pilsbot/pilsbot/hw-model/schalter_blende.FCStd

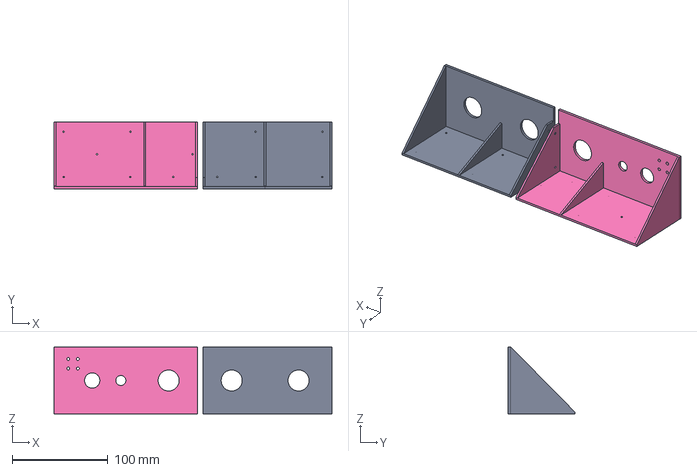
[picture p19: CAD file, 2021-12-27]
hw-model/schalter_blende.FCStd
291.0 x 70.0 x 70.0 mm
DingR
DingL
