pilsbot/pilsbot/hw-model/export/indicator_slots_base.stl

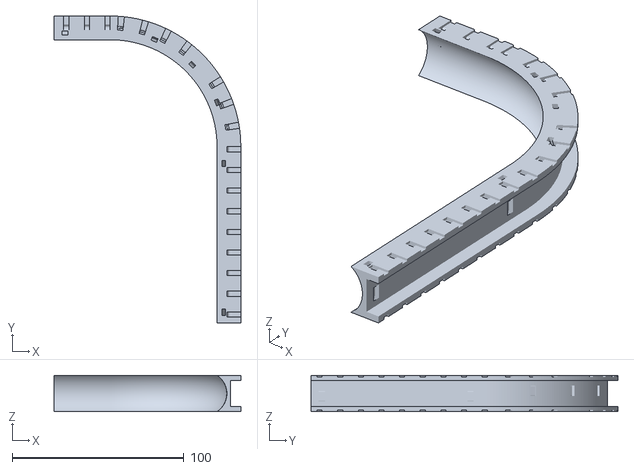
[picture p20: CAD file, 2025-06-03]
hw-model/export/indicator_slots_base.stl
108.5 x 178.5 x 21.0
