pilsbot/pilsbot/hw-model/head_mcu_case.FCStd

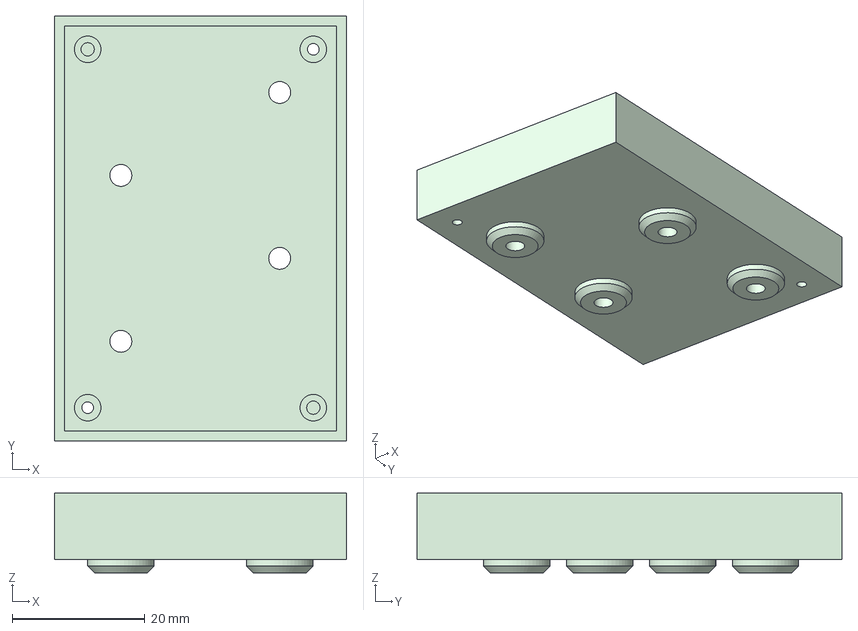
[picture p21: CAD file, 2021-06-11]
hw-model/head_mcu_case.FCStd
44.0 x 64.0 x 12.0 mm
