pilsbot/pilsbot/hw-model/export/indicator_slots_both.stl

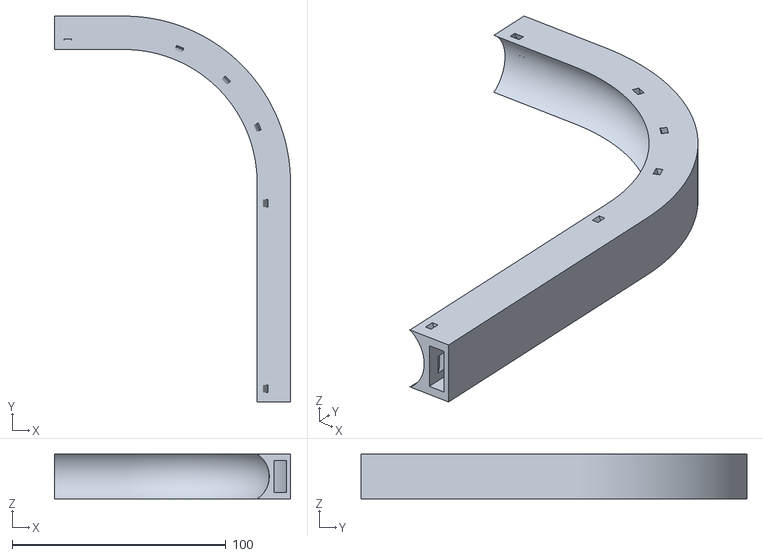
[picture p22: CAD file, 2025-06-03]
hw-model/export/indicator_slots_both.stl
110.3 x 180.3 x 21.0
