pilsbot/pilsbot/hw-model/export/axis_fastener.stl

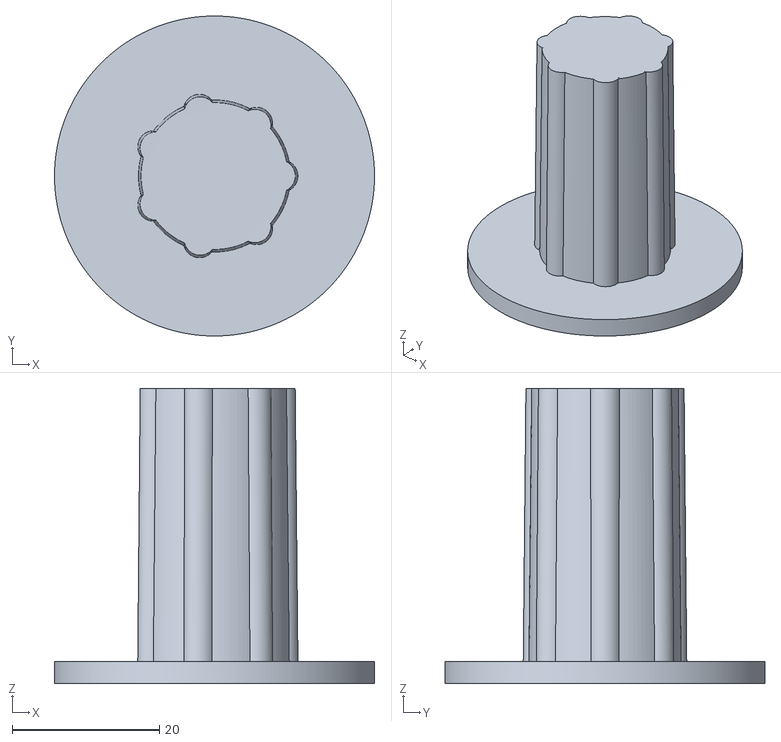
[picture p23: CAD file, 2024-06-01]
hw-model/export/axis_fastener.stl
43.5 x 43.5 x 40.1
