pilsbot/pilsbot/hw-model/export/SSD_holder_logging.stl

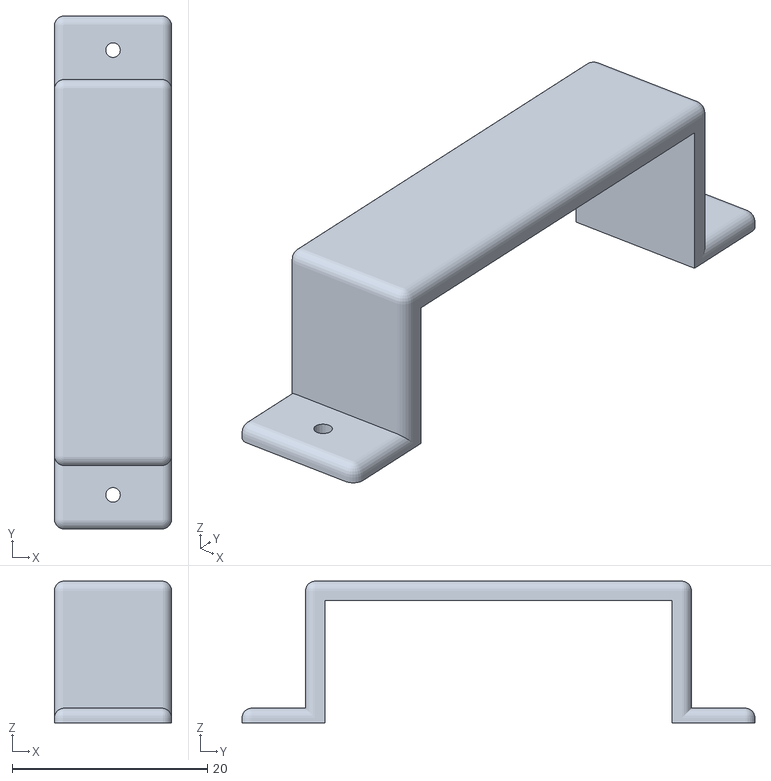
[picture p24: CAD file, 2024-06-01]
hw-model/export/SSD_holder_logging.stl
12.0 x 52.5 x 14.5
