pilsbot/pilsbot/hw-model/export/button_holder.stl

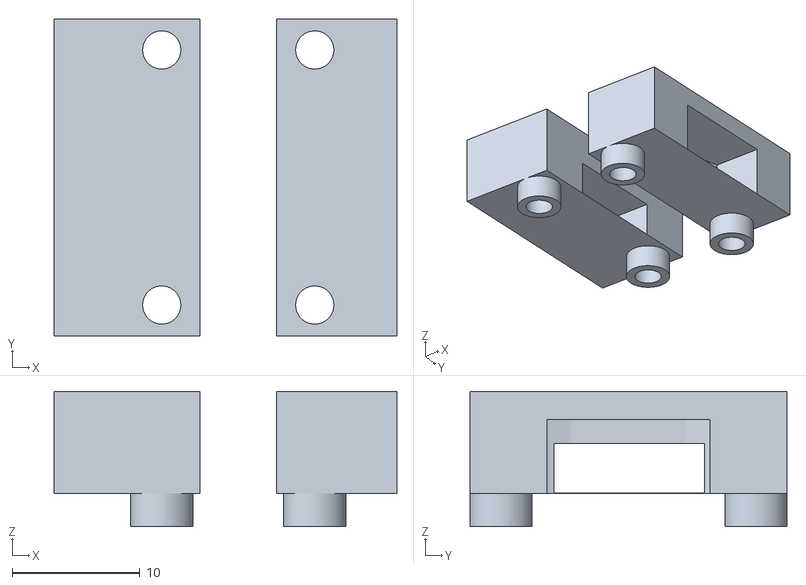
[picture p25: CAD file, 2024-06-01]
hw-model/export/button_holder.stl
26.9 x 24.9 x 10.6
