pilsbot/pilsbot/hw-model/export/antigriff.stl

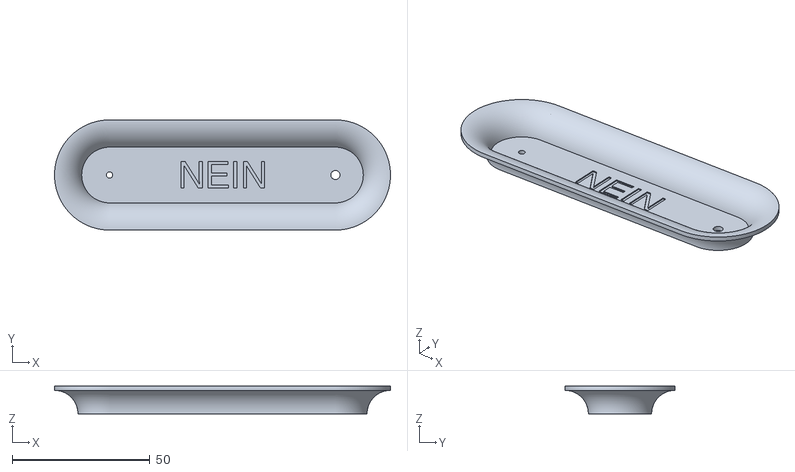
[picture p26: CAD file, 2024-03-05]
hw-model/export/antigriff.stl
122.0 x 40.0 x 10.0
