pilsbot/pilsbot/hw-model/export/steering_encoder_außen.stl

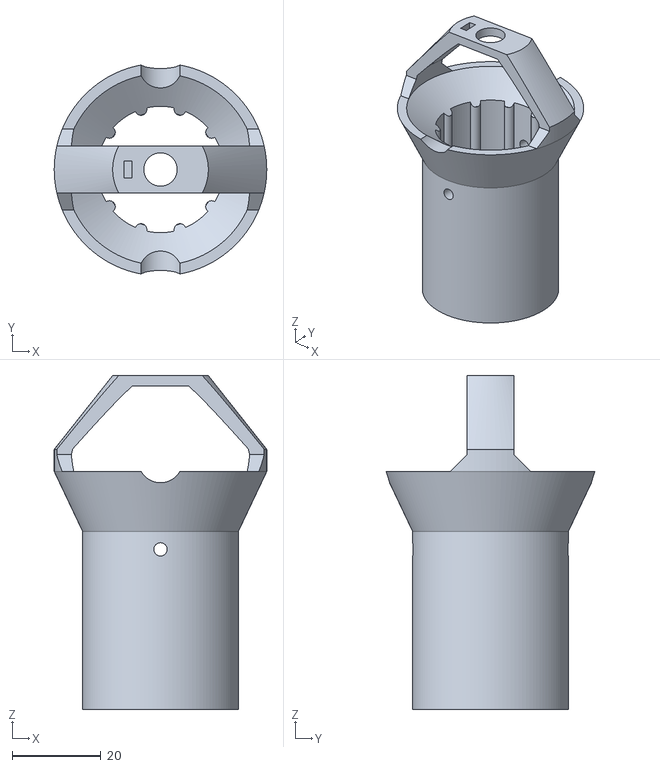
[picture p27: CAD file, 2023-06-13]
hw-model/export/steering_encoder_außen.stl
47.8 x 47.0 x 75.1
