pilsbot/pilsbot/hw-model/export/SSD_holder_root.stl

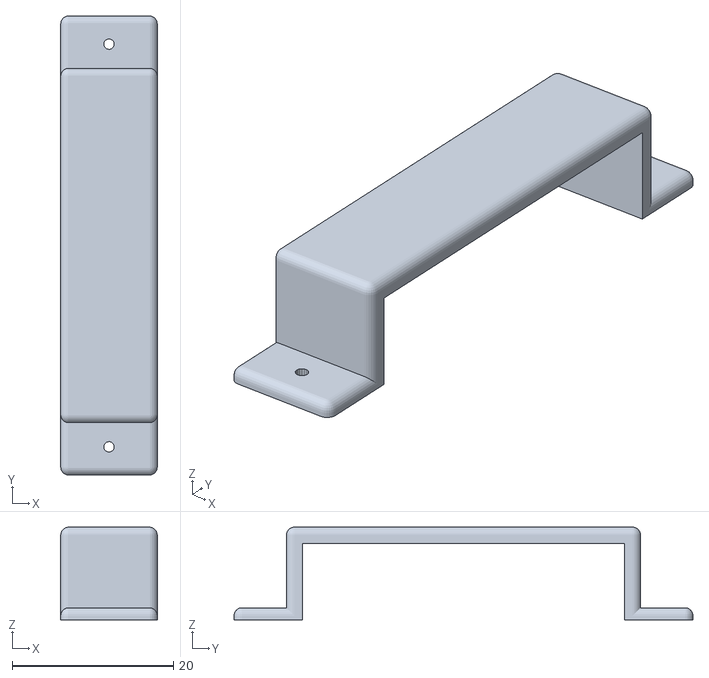
[picture p28: CAD file, 2023-02-14]
hw-model/export/SSD_holder_root.stl
12.0 x 57.0 x 11.5
