pilsbot/pilsbot/hw-model/export/splash_protection_hb_driver-Abdeckung.stl

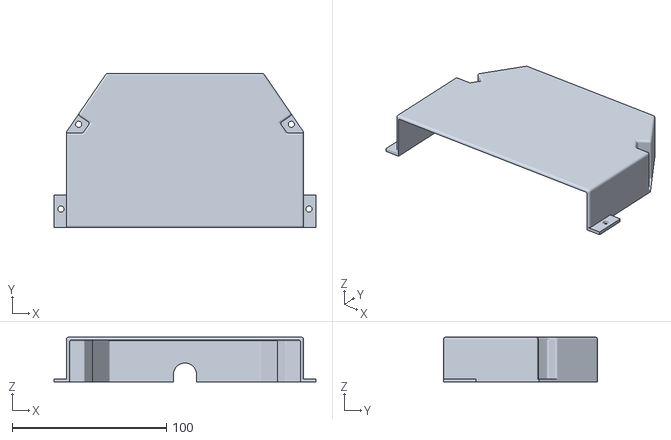
[picture p29: CAD file, 2023-02-14]
hw-model/export/splash_protection_hb_driver-Abdeckung.stl
170.0 x 100.0 x 29.0
