pilsbot/pilsbot/hw-model/export/Raspi-Cam-holder-Deckel.stl

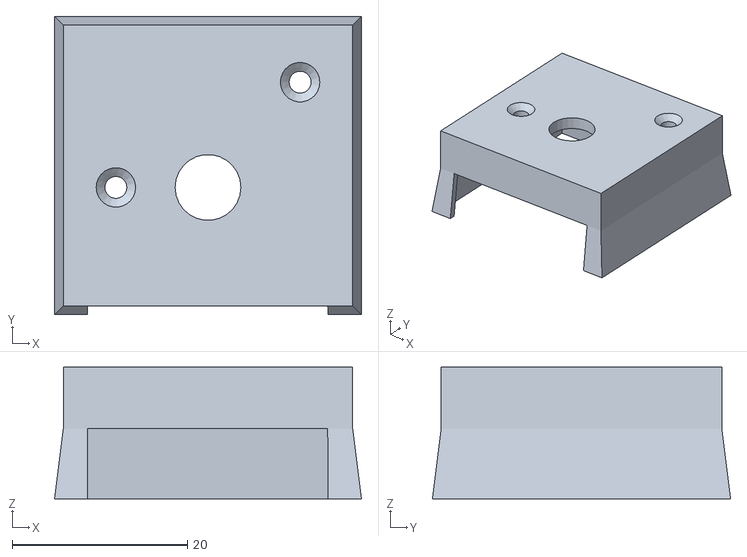
[picture p30: CAD file, 2023-01-29]
hw-model/export/Raspi-Cam-holder-Deckel.stl
35.0 x 34.0 x 15.0
