pilsbot/pilsbot/hw-model/export/water_splash_plate_holder.stl

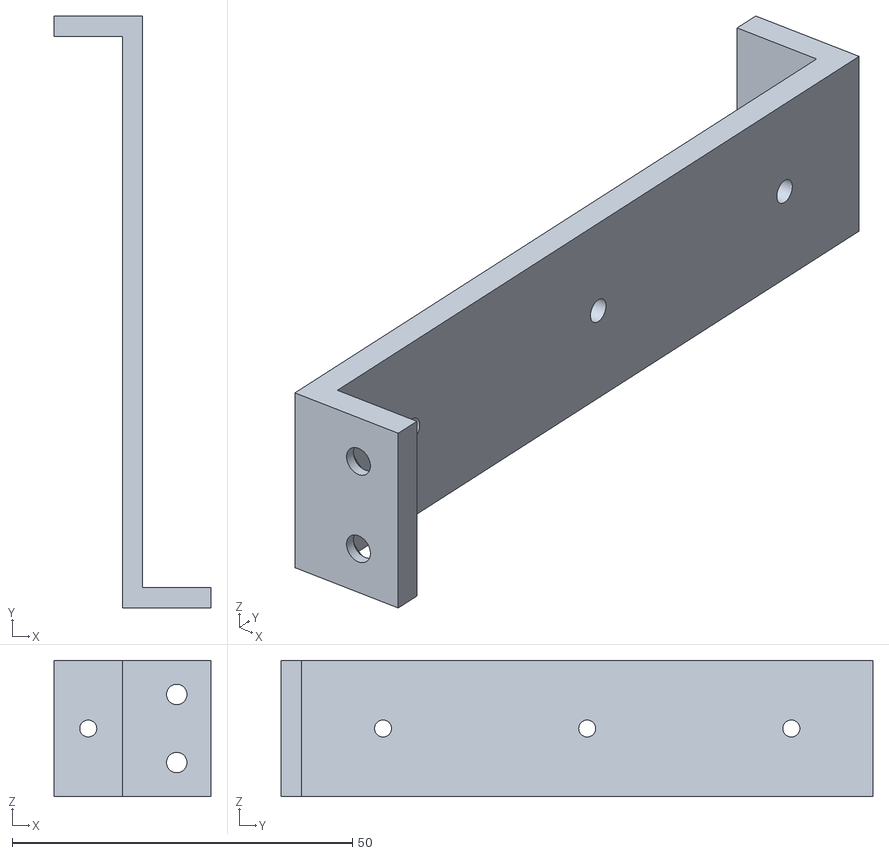
[picture p31: CAD file, 2023-01-28]
hw-model/export/water_splash_plate_holder.stl
23.0 x 87.0 x 20.0
