pilsbot/pilsbot/hw-model/export/bigbattery_holder_front.stl

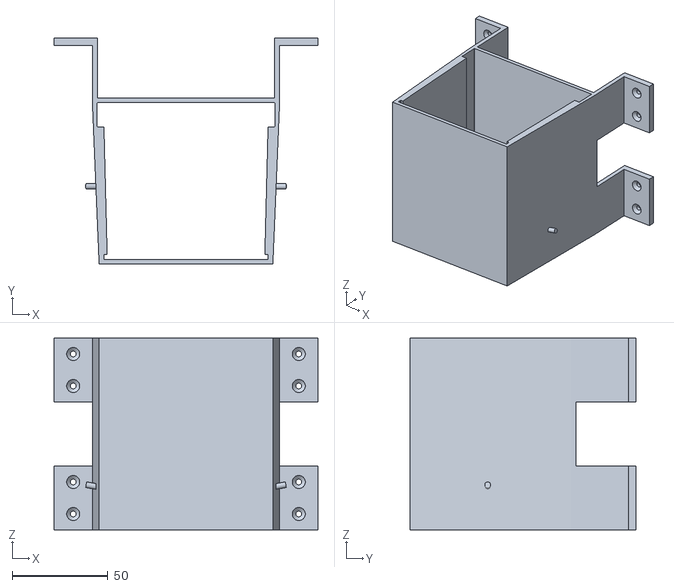
[picture p32: CAD file, 2023-01-28]
hw-model/export/bigbattery_holder_front.stl
137.5 x 117.8 x 100.0
