pilsbot/pilsbot/hw-model/export/bigbattery_holder_back.stl

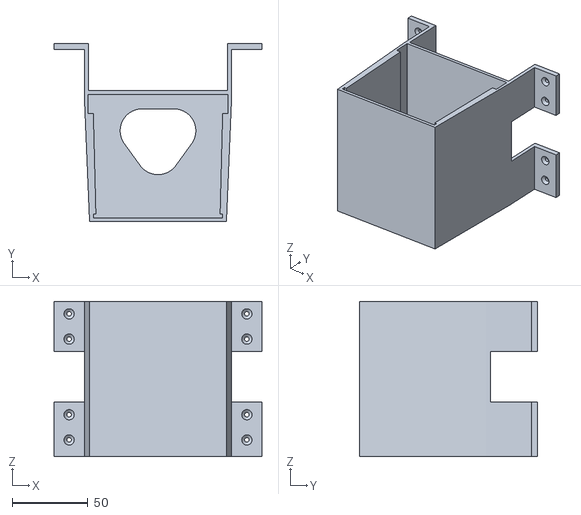
[picture p33: CAD file, 2023-01-28]
hw-model/export/bigbattery_holder_back.stl
137.5 x 117.8 x 102.8
