pilsbot/pilsbot/hw-model/export/battery_cable_strain_protector.stl

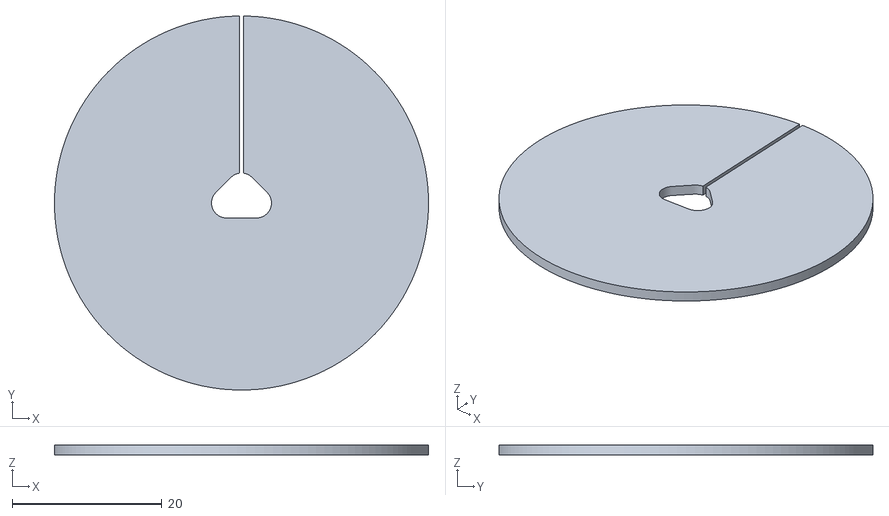
[picture p34: CAD file, 2023-01-21]
hw-model/export/battery_cable_strain_protector.stl
50.0 x 50.0 x 1.40
