pilsbot/pilsbot/hw-model/export/OAK-D_Mount.stl

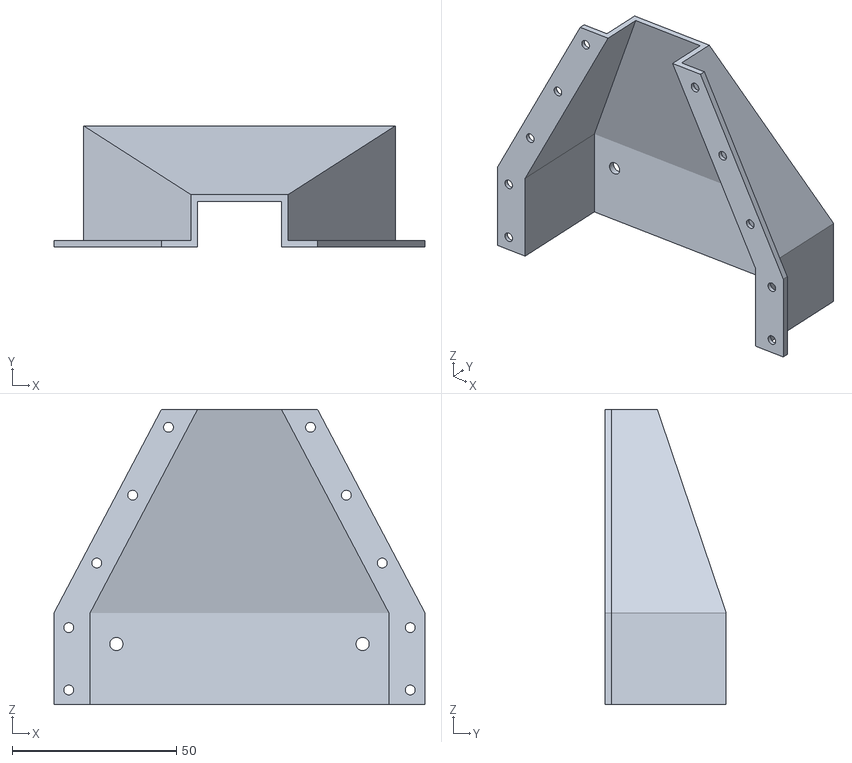
[picture p35: CAD file, 2023-01-19]
hw-model/export/OAK-D_Mount.stl
113.0 x 37.0 x 90.0
