pilsbot/pilsbot/hw-model/export/Raspi-Cam-holder-Counter_ding.stl

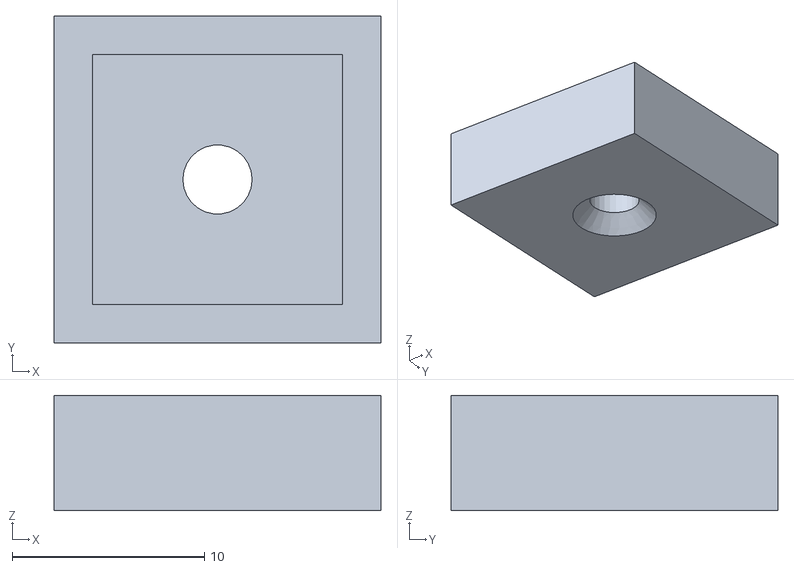
[picture p36: CAD file, 2023-01-08]
hw-model/export/Raspi-Cam-holder-Counter_ding.stl
17.0 x 17.0 x 6.00
