pilsbot/pilsbot/hw-model/export/joystick_receiver_holder.stl

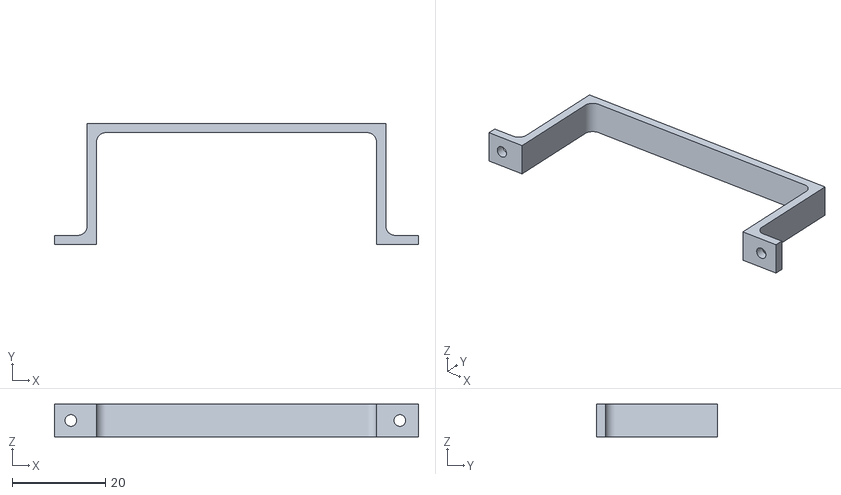
[picture p37: CAD file, 2023-01-08]
hw-model/export/joystick_receiver_holder.stl
78.0 x 26.0 x 7.00
