pilsbot/pilsbot/hw-model/export/steering_encoder_innen.stl

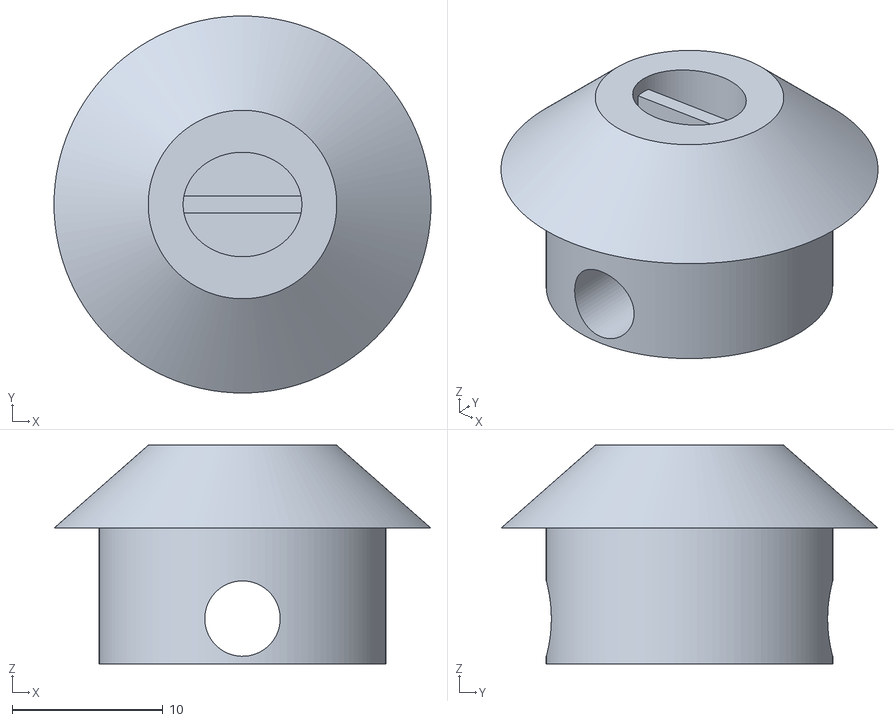
[picture p38: CAD file, 2022-03-26]
hw-model/export/steering_encoder_innen.stl
25.0 x 25.0 x 14.5
