pilsbot/pilsbot/hw-model/export/mountplate_feet.stl

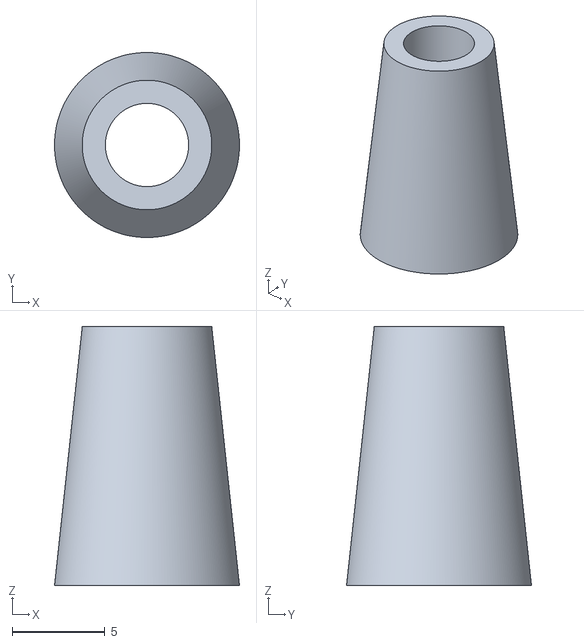
[picture p39: CAD file, 2022-03-26]
hw-model/export/mountplate_feet.stl
10.0 x 10.0 x 14.0
