pilsbot/pilsbot/hw-model/export/schalterblendeR.stl

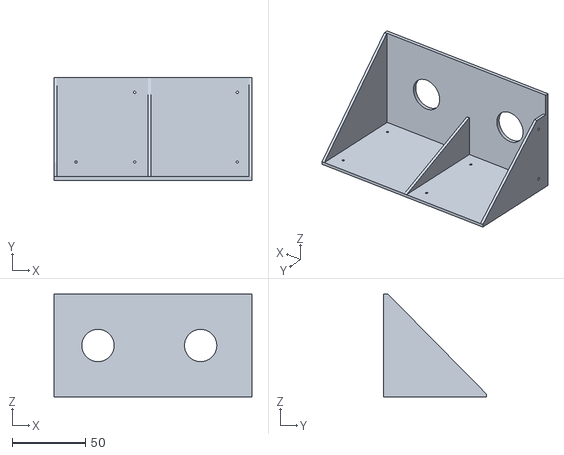
[picture p40: CAD file, 2021-12-27]
hw-model/export/schalterblendeR.stl
135.0 x 70.0 x 70.0
