pilsbot/pilsbot/hw-model/export/schalterblendeL.stl

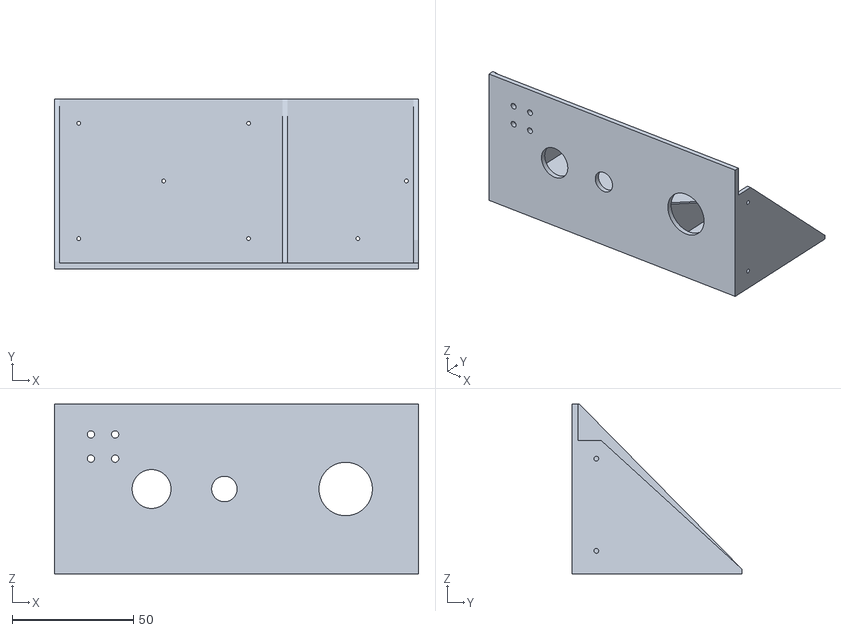
[picture p41: CAD file, 2021-12-27]
hw-model/export/schalterblendeL.stl
150.0 x 70.0 x 70.0
