pilsbot/pilsbot/hw-model/export/fix_steering_axle.stl

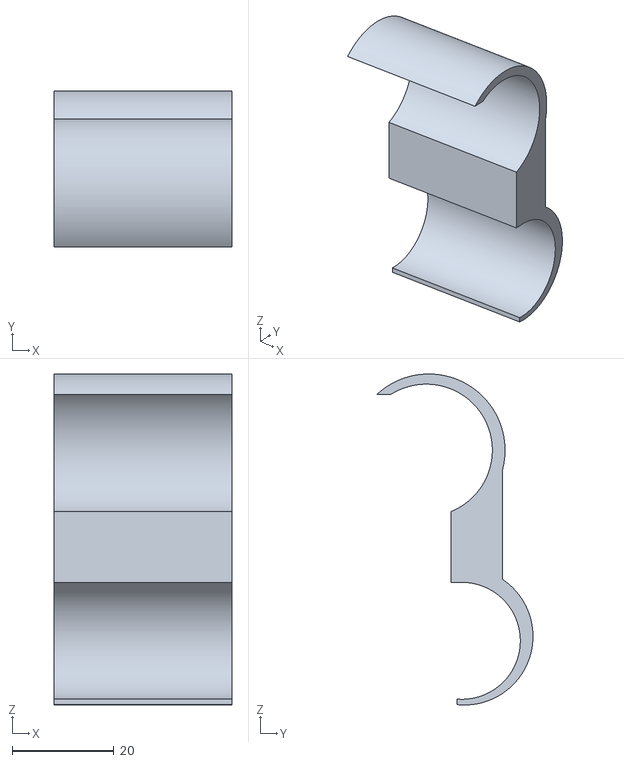
[picture p42: CAD file, 2021-12-26]
hw-model/export/fix_steering_axle.stl
35.0 x 30.7 x 65.1
