pilsbot/pilsbot/hw-model/export/upright_stand.stl

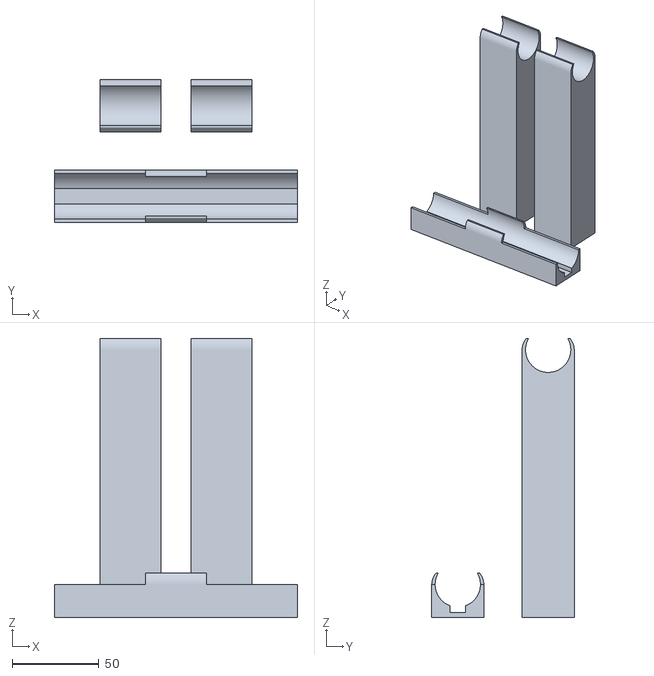
[picture p43: CAD file, 2021-11-18]
hw-model/export/upright_stand.stl
140.0 x 82.0 x 160.5
