pilsbot/pilsbot/hw-model/export/upright_stand_only_high_stand.stl

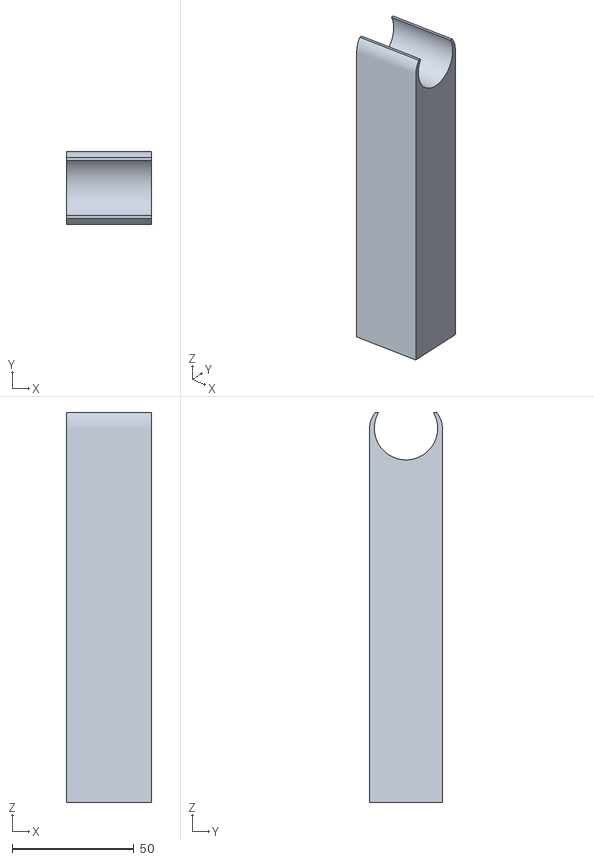
[picture p44: CAD file, 2021-11-18]
hw-model/export/upright_stand_only_high_stand.stl
35.0 x 30.0 x 160.5
