pilsbot/pilsbot/hw-model/export/battery_holder.stl

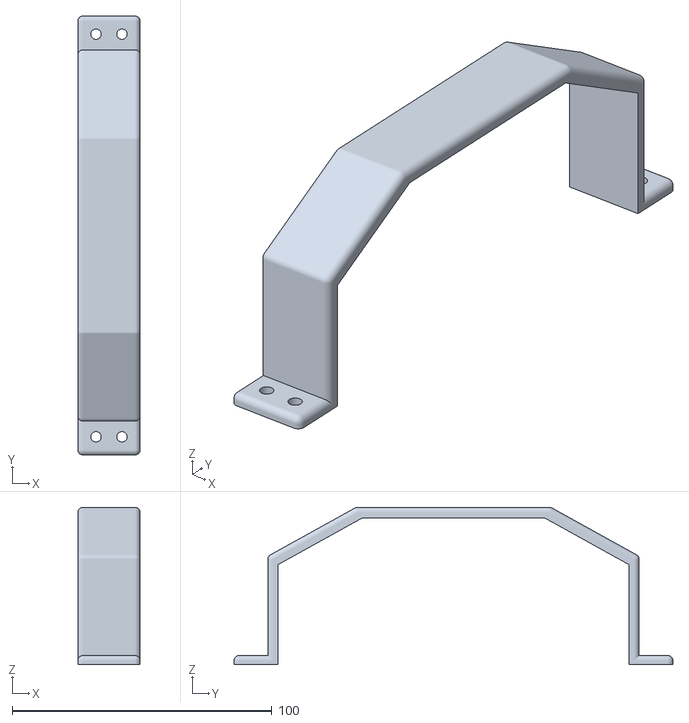
[picture p45: CAD file, 2020-07-17]
hw-model/export/battery_holder.stl
24.0 x 169.0 x 60.5
