pilsbot/pilsbot/hw-model/export/powerbank_holder.stl

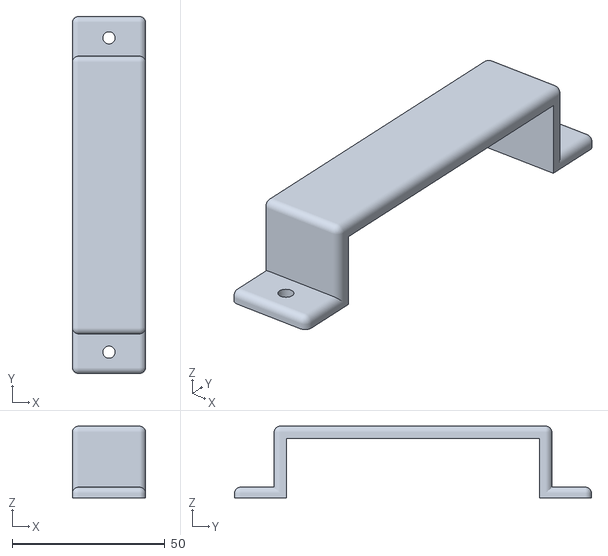
[picture p46: CAD file, 2020-07-12]
hw-model/export/powerbank_holder.stl
24.0 x 117.0 x 23.5
