pilsbot/pilsbot/hw-model/export/achse_abstandshalter.stl

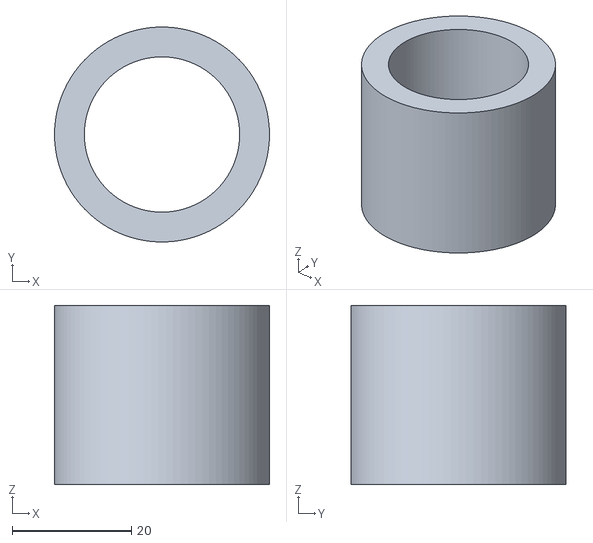
[picture p47: CAD file, 2020-05-30]
hw-model/export/achse_abstandshalter.stl
36.0 x 36.0 x 30.0
