pilsbot/pilsbot/hw-model/export/Achsadapter.stl

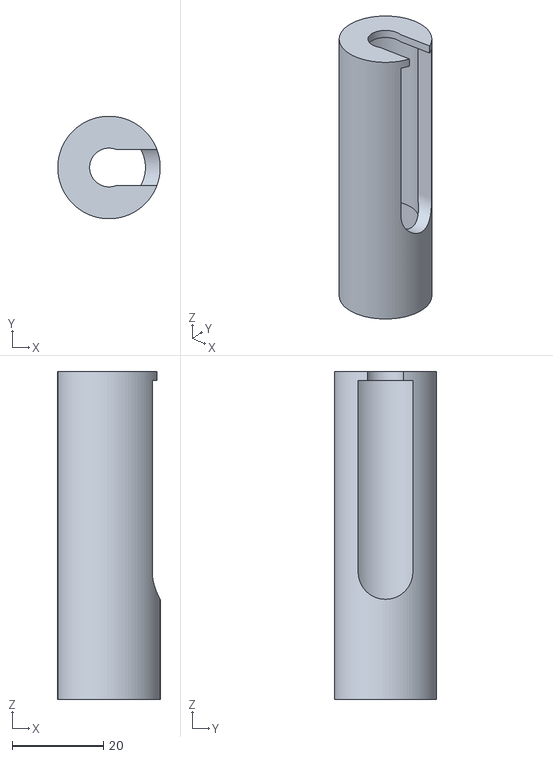
[picture p48: CAD file, 2020-05-30]
hw-model/export/Achsadapter.stl
22.5 x 22.5 x 72.0
