pilsbot/pilsbot/hw-model/export/pilsbot.stl

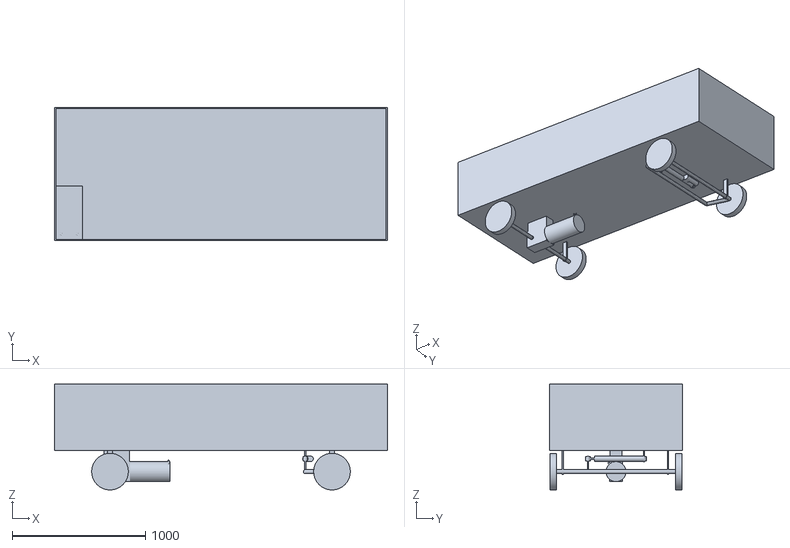
[picture p49: CAD file, 2019-08-15]
hw-model/export/pilsbot.stl
2500.0 x 1000.0 x 795.0
