pilsbot/pilsbot/hw-model/main_plate_clamp.scad

chassis_tube_d = 25;	//TODO: Check
diff = 26;			// Measured from plate to top point of tube
breite = 23;
sdriver_clearance = 13;
absatz_h = 7;
screw_d = 5;

base_h = diff-chassis_tube_d/2;
$fn = $preview ? 80 : 200;

difference(){
	union(){
		translate([0,0,base_h])
			rotate([-90, 0,0]) difference(){
				cylinder(r=breite, h=breite);
				translate([-breite, 0,-.5])
					cube([breite*2, breite, breite+1]);
				
				//the tube
				translate([-chassis_tube_d/2,0,-.5])
					#cylinder(d=chassis_tube_d, h=breite+1);
			}
		cube([breite, breite, base_h]);
	}
	//the screw hole
	translate([breite/2, breite/2,0]){
		translate([0,0, absatz_h])
			cylinder(d1=sdriver_clearance-1, d2=sdriver_clearance+3, h=base_h+breite-absatz_h);
		cylinder(d=4.5, h=100);
	}
}
