pilsbot/pilsbot/hw-model/mountplate_feet.scad

$fn = 200;

h = 9+5;

difference(){
	cylinder(d1 = 10, d2 = 7, h = h);
	cylinder(d = 4.5, h = h+1);
}
